shirriff/alto-disk-interface/TestApp/diablo.c

/* GIMP RGBA C-Source image dump (diablo.c) */

static const struct {
  unsigned int 	 width;
  unsigned int 	 height;
  unsigned int 	 bytes_per_pixel; /* 2:RGB16, 3:RGB, 4:RGBA */ 
  unsigned char	 pixel_data[240 * 83 * 2 + 1];
} banner = {
  240, 83, 2,
  "\356\203\371\346x\326\214{\303A\040\071\000\071\243A\244AA\061B\061\245\071\245A"
  "\305A\006J\006J\305A\305A\006J'RGR\210R\210Z\250Z\251Z\311b\352b\251Z\251Z\351"
  "b\351b\351b\351b\351b\351b\351b\311b\351b\012k\012k*k+s*k*sKsKsKsKsKsKsKsk"
  "s*k\011k\011k*k\011s*s*s\011k\011k\011k\011k\351j\351j*s*s*s\011s\011s*s*s*s*s*s*"
  "s*sJ{J{K{k{*{J{J{J{K\203k{\213{\213{\213{\253\203\213\203k{k{\254\203\254"
  "\203\254\203\254\203\214{\213\203\214\203\214{k{\214\203\315\203\315\213"
  "\254\203\214{\254\203\254\203\254\203\314\203\315\203\315\203\315\203\315"
  "\203\355\213\315\203\254\203\315\203\315\203\315\203\315\203\355\203\254"
  "\203\214{\254\203\254\203\214{\215{\255{\215{\214{l{\214{\215{ls+k\012k\312"
  "b\311Z\311Z\311Z\311Z\251ZHR\346A\006B'J\346A\006B\006J\006J\006J\006B\006J\346A\245\071"
  "\305A\346A\346A'J\006J\346A\245A\245\071\305A\346A\345A\305A\305\071\305A\245"
  "A\306I\306I\346I\346A\306A\306A\305A\305A\305A\245A\245A\245Ad\071d\071d\071"
  "C\071\003\061#\071\003\071#\071A\061\000)\040\061\000\061@\040\240(\240(\200(`\040\040\040\200"
  "\040\001\040\040\040@\040\000\030\000\000\000\000\000\000\000\000\000\000\000\000\000\000\000\000\000\000\000\000\000\000\000\000\000"
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
  "N[N[N[N[N[N[N[N[N[N[N[N[N[N[N[N[N[N[N[N[N[N[N[N[N[.[.[.[.[.[.[.[.[.[.[.["
  ".[.[.[.[.[.[.[.[.[.[.S.[O[O[.[\015SkBg!\001\000g!\217cs\204\260k\350\071E!e)\246"
  "\071\006B'JGJ'B\245\071\315\203\322\244\261\234D\061\013[u\255\225\265\013c\000\000"
  "\000\000\000\000\000\000\000\000\000\000N[n[n[n[\217coco[o[n[o[o[N[N[N[N[N[N[N[N[N[N[N[NS.S."
  "S.S.S.S.S.S.S.S.SNSoSoSoSo[NSNSNSNSNSNSNSNSNSNSOS.S.S.S.S.SO[O[N[.S.S\016"
  "S.SN[N[O[O[N[NSNSNSo[o[o[n[nSnSNSN[O[O[o[o[o[o[o[o[o[o[n[nSNSn[o[n[n[n[n"
  "[n[n[o[o[O[N[n[o[o[n[n[o[N[N[N[N[O[O[O[O[o[O[o[O[N[N[N[N[o[o[o[o[o[o[\217"
  "[o[o[n[n[o[o[o[n[n[o[o[o[n[N[n[o[o[o[o[o[o[o[o[o[o[n[N[N[N[N[N[N[N[N[N[N"
  "[N[n[N[N[N[N[N[N[N[N[N[N[N[N[n[n[.[N[.[.[.[.[.[.[.[.[.[-[-[.[.[.[.[.[.[."
  "[.[.[.S.[N[.[\355JJ:\003\000'\031\355R.[N[\015S\350\061\347\071\010B'J'JGJ\210RHJ"
  "\305A\315\203\322\244\261\234\342\040\353Z\225\255t\255\313Z\000\000\000\000\000\000\000"
  "\000\000\000B\000\217co[\217c\217c\257c\217cn[n[n[O[O[n[n[n[N[N[NSNSNSNSNSNSNSNS"
  "NSNS.SNSNSNSNSNSNSNSNSNSNSNSNSNSNSNSNSNSNSNSNSNSNSNSNSNSNSNSNSNSNSNS.S.S"
  ".S.S.S.SNSNSNSNSNSNSNSNSNSOSoSoSOSoSoSo[o[OSOSOSo[o[o[o[o[o[O[O[O[o[o[o["
  "n[o[o[o[o[o[o[NSNSo[o[o[O[NSN[N[o[o[NSNSo[o[n[o[o[o[o[o[n[n[o[o[o[o[n[o["
  "o[o[o[o[o[o[o[o[o[o[o[o[o[o[o[o[o[o[o[o[o[o[o[o[o[o[o[o[o[o[o[o[o[o[o[o["
  "o[o[o[o[o[n[n[n[n[n[n[n[n[n[n[N[N[N[N[N[N[N[N[N[N[.[.[.[.[.[.[.[.[.[.[N["
  "N[.[.S.S\015S\315JK:\006\011*:\355R\015S\015S\015S):\307\071\010BhRhR\210R\251ZhR"
  "\006B\315\203\322\244\261\234\342\040\312Zu\255\225\265\013c\000\000\000\000\000\000\000\000"
  "\000\000\000\000\355R\355R\355R\314J\314J\015S\015S\355J.[N[.[n[N[-S\015S.[.S-S-S-S"
  "-S.S.S.S.S.S.S.S-S.S.[NSNS.SNS.SNSNS.S.S.S.S.S.S.SNSNSNSNSNSNSNSNSNS.S.S"
  ".SNS.S.S.S.S.S.S.S.S.SNSNSNK.K.KNSNSoSoSOSOSOSOSOSOSOSoSoSOSoSo[o[o[O[O["
  "O[O[O[N[N[NSOSoSo[o[o[o[o[oSoSOSOSnSnSnSo[o[o[o[o[o[o[o[o[o[o[o[o[o[o[o["
  "o[o[\217[\217[\217[\217[\217[\217[o[o[o[n[o[o[\217[o[o[o[o[o[o[o[o[o[o[o"
  "[o[o[o[o[o[\217[\217[\217[o[o[o[o[o[o[o[o[o[o[o[o[o[n[n[o[N[N[N[n[n[o[N["
  "N[N[.[N[N[N[N[N[N[N[N[N[N[N[N[N[N[N[N[N[N[N[\016S\355R\315J\254J*\062J:\314"
  "J\355R-[N[IBe)\007BHR\251Z\251ZhZ\251Z'J\356\203\261\234\261\234#)\211RT\255"
  "\225\265,k\000\000\000\000\000\000\000\000\000\000\000\000\210!\351\061J:\314J\253J):g\031\245\000g!"
  "J:\254J\354R\015S-[.[-[-[-S-S-S\015S-S-S-S-S-S-S-[-S-S\015S\015S\015S\015S\015S"
  "-S-S-S.S.S.S.S.S-S-S-S-SMSNS.S.S.S.S.S-K-K-K.K.KNK-K-K.KNKNS-K-S-S-S-S-S"
  "-S.S.S-S.S.S.SNSNSNSNSN[O[O[O[O[O[O[O[o[o[O[N[N[N[N[NSoSOSNSNSNSOSNSNSNS"
  "NSNSnSnSnSnSnSnSnSnSnSoSo[o[n[o[n[N[n[n[o[n[o[o[o[o[o[oco[o[O[O[O[o[\217"
  "[o[o[o[o[o[o[o[o[o[o[\217[o[n[N[o[\217cococn[o[o[o[o[O[N[o[o[o[o[o[o[n[n"
  "[n[N[n[n[n[n[n[N[n[ncn[n[N[N[n[N[N[N[N[N[N[N[N[N[N[N[N[N[N[N[N[N[-S\314J"
  "\253J\354R\314J\253J\213B\254J\354R\354RIB\004\031\205\061HJ\251ZiR\007JhRGR/\214"
  "\261\234\261\234d\061iRT\255T\255,c\000\000\000\000\000\000\000\000\000\000\005\031\354R\354R\015"
  "S\355R\015[\355Z\314J\011\062\002\000\204\000\253B\253J\253J\355R-[-[\015S\014S\014S"
  "\014S\015S\015S\015S\015S\015S\015S\015S\015S\015S\015S\355R\355R\355R\354J\354J\354"
  "R\015S\015S\015S\015S\015S\015S\015S\015S\015S-S-SNSNS-S-S.S\015S\015S-S-K\015K\015K\015"
  "K\015K-K-K-K-K-K-K\015S\015S\015S\015S\015S\355J\015S\015S\015S\015S\015S\015S-S-S-S"
  "NSN[N[N[N[n[n[n[n[n[n[nSnSn[n[\216[\217[n[N[NSN[n[n[N[N[N[NSNSNS.SNSNSN["
  "N[N[N[N[N[n[n[n[N[N[n[ocococncoc\217cocococnc\217c\217c\217cococ\217c\217"
  "c\217c\217c\217c\217c\217c\217c\217c\217c\217c\217c\217c\217c\217c\217c\217"
  "c\217c\217c\217cncncococococncncncN[N[ncocncncncncncN[N[N[n[ncncNcncncnc"
  "ncncncNcN[N[N[N[N[N[.[N[N[M[-[-[-[-[n[-[\314R\213BjB\253J\314R\355R\015S\354"
  "R\313RiB$!e)'B\211RHR\245A'JhR/\214\261\234\221\234d\061\211RT\255\064\245"
  "\013c\000\000\000\000\000\000\000\000\000\000\000\000\207)\310\061\247)\310\061\310\061\310\061\247)\244"
  "\000\305\000\311\061\011\062J:jB\213B\253J\212B\313J\314J\314J\314J\314J\314J\354"
  "R\354R\354R\354R\354R\354R\354R\354R\014S\015[\015S\015[\015[-[-[-[\015S\015S\015"
  "S\015S\015S-S-[-S-[-S-S-[-[.[.S.S-S-[-[-[-[M[N[n[n[n[n[ncncncNcNcncnc\216c"
  "ncnc\217c\217k\257c\257k\257k\257k\257k\317k\317k\320k\320k\320k\320k\320"
  "k\320k\360k\320k\360k\360k\360k\360k\360k\357k\320k\320s\360s\360s\360s\020"
  "t\360s\360s\360s\360s\317k\317k\320s\360s\360s\360s\360s\020t\020t\021t\061t"
  "\021t\020t\020t\020t\020|\020t\020t\020|\021|\061|\061|Q|\061|\061|\061|\061|\061|R\204R"
  "\204r\204r\204r\204Q|Q|Q|\061|\061|Q|Q|Q|Q|\061|\061|\061|\061|\061|\021|\021|\360"
  "s\360s\320s\257k\257k\317k\257k\257k\257k\257k\257k\257k\257k\257k\217k\217"
  "k\257k\257k\217k\217k\217c\216c\216c\216c\216c\216cncncncncncncncncncncn"
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
  "\000\000\000\000\000\000\000\000\000\000\000\000\000\000\000\000\000\000\000\000\000\000\000\000\000\000\000\000\000\000\000\000\000\000\000\000"
  "\000\000\000\000\000\000\000\000\000\000\000\000\000\000\000\000\000\000\000\000\000\000\000\000\000\000\000\000\000\000\000\000\000\000\000\000"
  "\000\000\000\000\000\000\000\000\000\000\000\000\000\000\000\000\000\000\000\000\000\000\000\000\000\000\000\000\000\000\000\000\000\000\000\000"
  "\000\000\000\000\000\000\000\000\000\000\000\000\000\000\000\000\000\000\000\000\000\000\000\000\000\000\000\000\000\000\000\000\000\000\000\000"
  "\000\000\000\000\000\000\000\000\000\000\000\000\000\000\000\000\000\000\000\000\000\000\000\000\000\000\000\000\000\000\000\000\000\000\000\000"
  "\000\000\000\000\000\000\000\000\000\000\000\000\000\000\000\000\000\000\000\000\000\000\000\000\000\000\000\000\000\000\000\000\000\000\000\000"
  "\000",
};
