shirriff/alto-disk-interface/TestApp/load.c

/* GIMP RGBA C-Source image dump (load.c) */

static const struct {
  unsigned int 	 width;
  unsigned int 	 height;
  unsigned int 	 bytes_per_pixel; /* 2:RGB16, 3:RGB, 4:RGBA */ 
  unsigned char	 pixel_data[90 * 32 * 2 + 1];
} load = {
  90, 32, 2,
  "\231\326\231\326\231\326\231\326\231\326\231\326\231\326\231\326\231\326"
  "\231\326\231\326\231\326\231\326\231\326\231\326\231\326\231\326\231\326"
  "\231\326\231\326\231\326\231\326\231\326\231\326\231\326\231\326\231\326"
  "\231\326\231\326\231\326\231\326\231\326\231\326\231\326\231\326\231\326"
  "\231\326\231\326\231\326\231\326\231\326\231\326\231\326\231\326\231\326"
  "\231\326\231\326\231\326\231\326\231\326\231\326\231\326\231\326\231\326"
  "\231\326\231\326\231\326\231\326\231\326\231\326\231\326\231\326\231\326"
  "\231\326\231\326\231\326\231\326\231\326\231\326\231\326\231\326\231\326"
  "\231\326\231\326\231\326\231\326\231\326\231\326\231\326\231\326\231\326"
  "\231\326\231\326\231\326\231\326\231\326\231\326\326\275\357{\010B\231\326"
  "\271\326\332\336\373\346\373\346\373\346\373\346\373\346\373\346\373\346"
  "\373\346\373\346\373\346\373\346\373\346\373\346\373\346\373\346\373\346"
  "\373\346\373\346\373\346\373\346\373\346\373\346\373\346\373\346\373\346"
  "\373\346\373\346\373\346\373\346\373\346\373\346\373\346\373\346\373\346"
  "\373\346\373\346\373\346\373\346\373\346\373\346\373\346\373\346\373\346"
  "\373\346\373\346\373\346\373\346\373\346\373\346\373\346\373\346\373\346"
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
  "B\010B\010B\010B\010B\010B\010B\010B\010B\010B\010B\010B\010B\010B\010B\010B\010B\010B\010"
  "B\010B\010B\010B\010B\010B\010B\010B\010B\010B\010B\010B\010B\010B\010B\010B\010B\010B\010"
  "B\010B\010B\010B\010B\010B\010B\010B\010B\010B\010B\010B\010B\010B\010B\010B\010B",
};
