shirriff/alto-disk-interface/TestApp/arrow-down.c

/* GIMP RGB C-Source image dump (arrow-down.c) */

static const struct {
  unsigned int 	 width;
  unsigned int 	 height;
  unsigned int 	 bytes_per_pixel; /* 2:RGB16, 3:RGB, 4:RGBA */ 
  unsigned char	 pixel_data[32 * 32 * 2 + 1];
} arrowDown = {
  32, 32, 2,
  "\231\326\231\326\231\326\231\326\231\326\231\326\231\326\231\326\231\326"
  "\231\326\231\326\231\326\231\326\231\326\231\326\231\326\231\326\231\326"
  "\231\326\231\326\231\326\231\326\231\326\231\326\231\326\231\326\231\326"
  "\231\326\231\326\326\275\357{\010B\231\326\271\326\332\336\373\346\373\346"
  "\373\346\373\346\373\346\373\346\373\346\373\346\373\346\373\346\373\346"
  "\373\346\373\346\373\346\373\346\373\346\373\346\373\346\373\346\373\346"
  "\373\346\373\346\373\346\373\346\272\336X\316T\255\216s\010B\231\326\332\336"
  "]\357\276\367\276\367\276\367\276\367\276\367\276\367\276\367\276\367\276"
  "\367\276\367\276\367\276\367\276\367\276\367\276\367\276\367\276\367\276"
  "\367\276\367\276\367\276\367\276\367\276\367\276\367\034\347\266\275P\214"
  "\013c\010B\231\326\373\346\276\367\377\377\276\377\276\367\276\367\276\367"
  "\276\367\276\367\276\367\276\367\276\367\276\367\276\367\276\367\276\367"
  "\276\367\276\367\276\367\276\367\276\367\276\367\276\367\276\367\276\367"
  "\276\367\373\336U\255\216s\212R\010B\231\326\373\346\276\367\276\377\\\357"
  "\373\346\373\346\373\346\373\346\373\346\373\346\373\346\373\346\373\346"
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
  "R\252R\252R\252R\252R\252R\252R\252R\252R\252R\252R\252R\252R\252R\252R\252"
  "R\252R\252R\212R(B\010B\010B\010B\010B\010B\010B\010B\010B\010B\010B\010B\010B\010B\010"
  "B\010B\010B\010B\010B\010B\010B\010B\010B\010B\010B\010B\010B\010B\010B\010B\010B\010B\010"
  "B\010B",
};
